kayfooi/ECE4191_T26/CV/checkerboard/checkerboard1.png

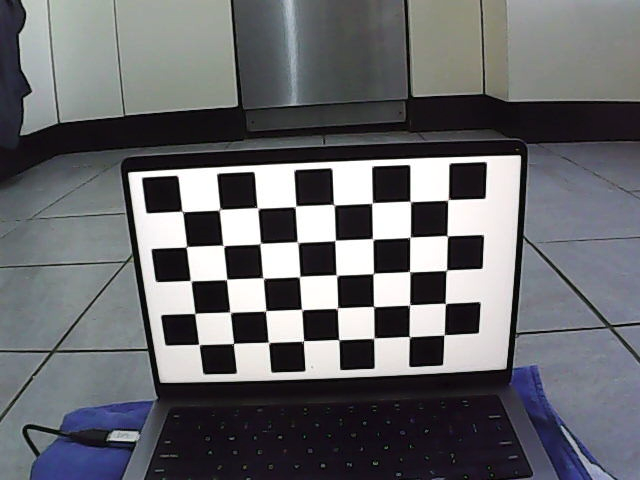
CV/checkerboard/checkerboard1.png
