kayfooi/ECE4191_T26/CV/checkerboard/checkerboard2.png

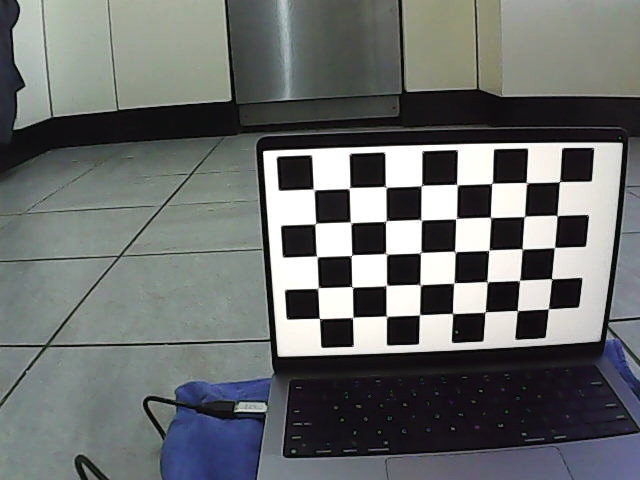
CV/checkerboard/checkerboard2.png
