kayfooi/ECE4191_T26/CV/checkerboard/checkerboard3.png

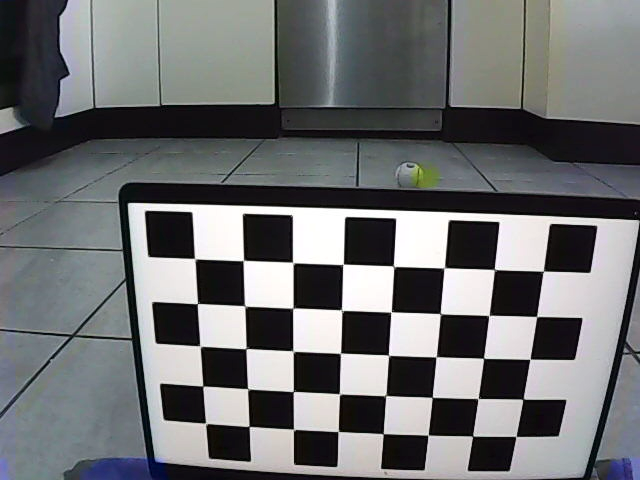
CV/checkerboard/checkerboard3.png
