kayfooi/ECE4191_T26/CV/checkerboard/checkerboard.png

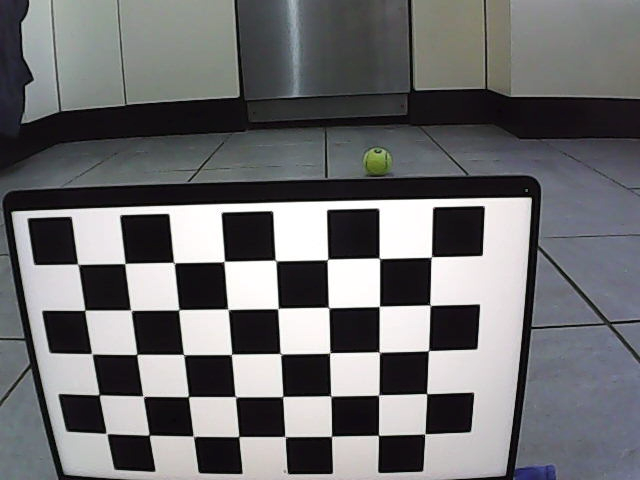
CV/checkerboard/checkerboard.png
