kayfooi/ECE4191_T26/EncoderExplanation for Provided Motor.PNG

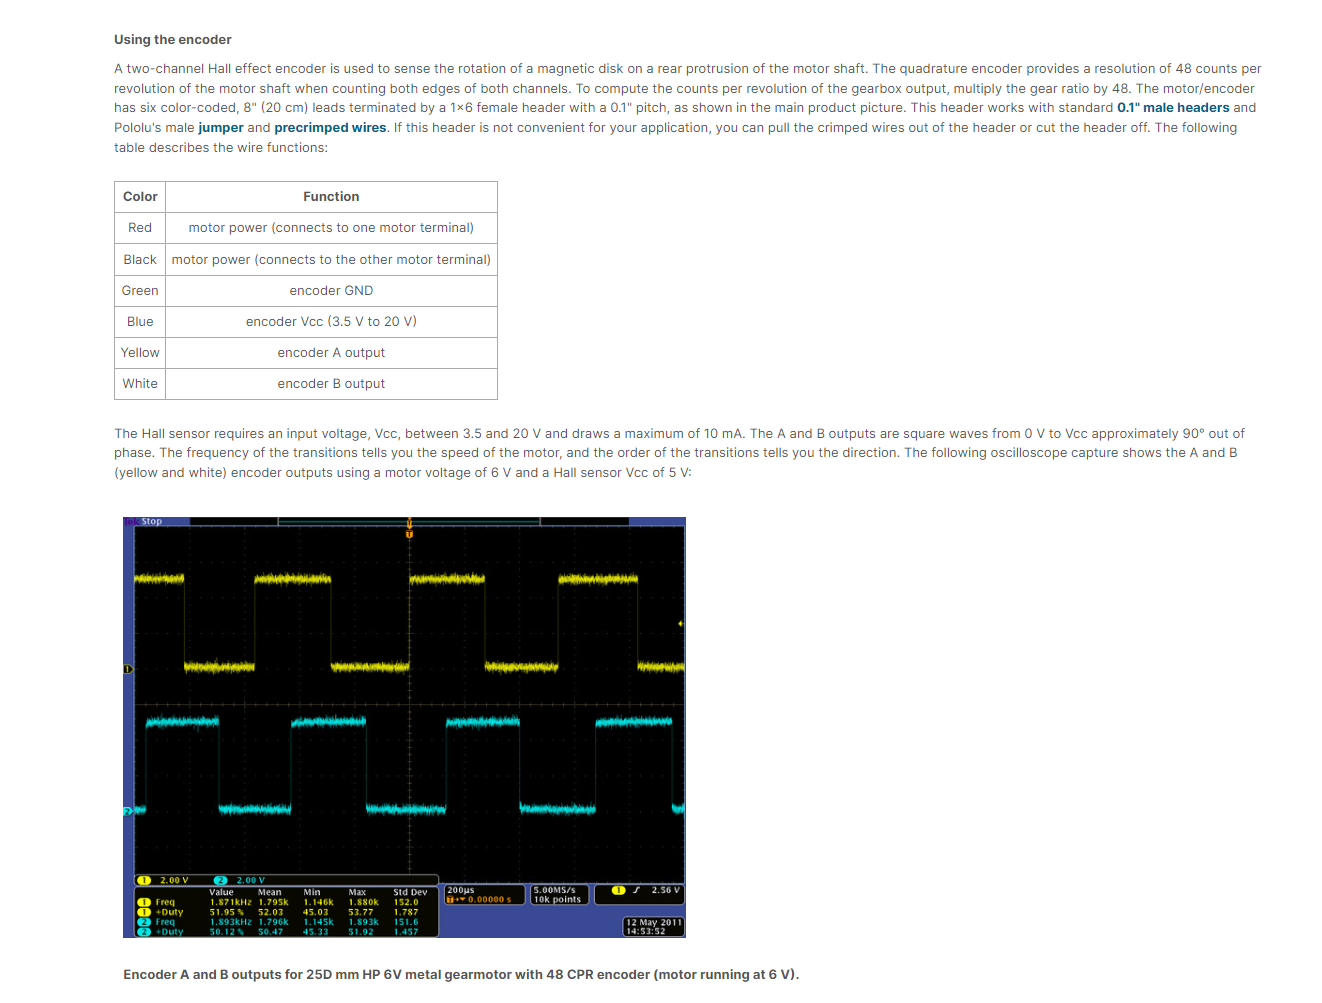
EncoderExplanation for Provided Motor.PNG
