kayfooi/ECE4191_T26/CV/calibration_img.png

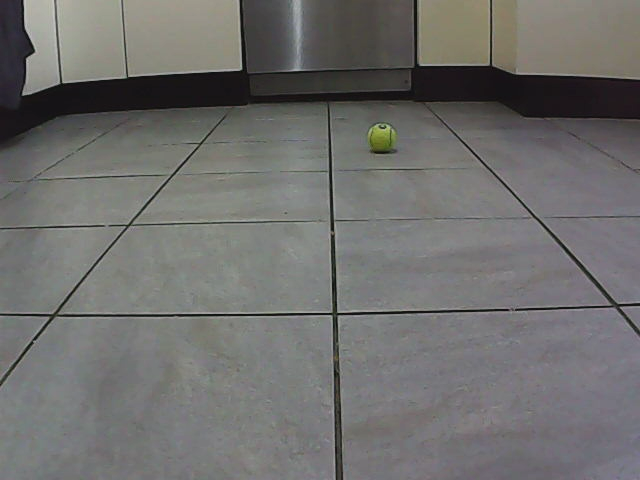
CV/calibration_img.png
