kayfooi/ECE4191_T26/CV/test_imgs/box/0001.jpg

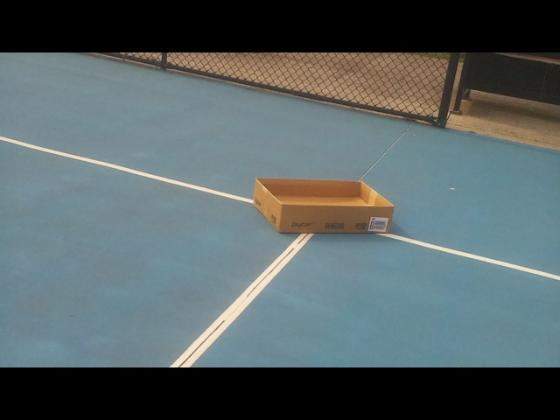
CV/test_imgs/box/0001.jpg
