kayfooi/ECE4191_T26/CV/test_imgs/box/0002.jpg

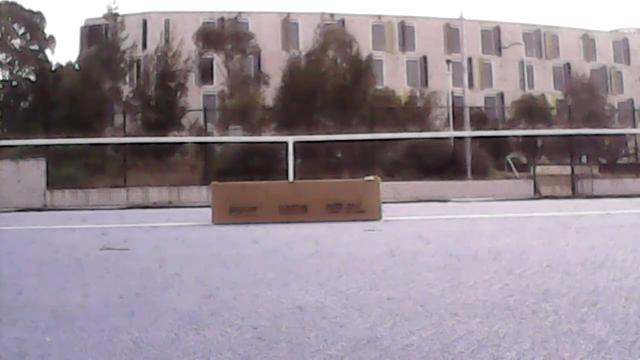
CV/test_imgs/box/0002.jpg
