kayfooi/ECE4191_T26/CV/white_line_detection_result.jpg

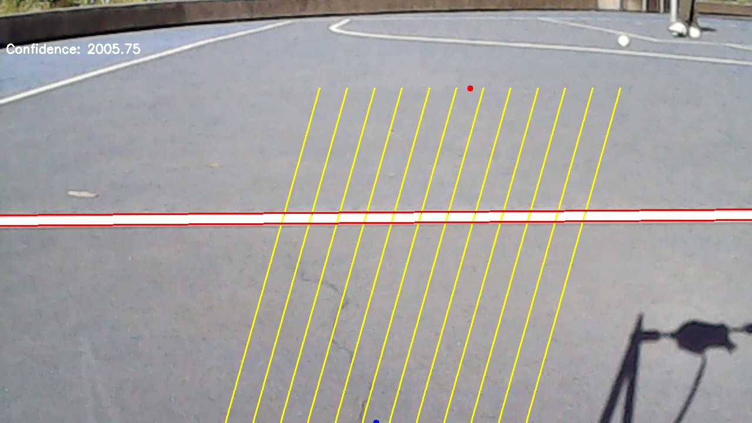
CV/white_line_detection_result.jpg
