kayfooi/ECE4191_T26/test_results/1728355701/line_detect_192_100_200_peaks.jpg

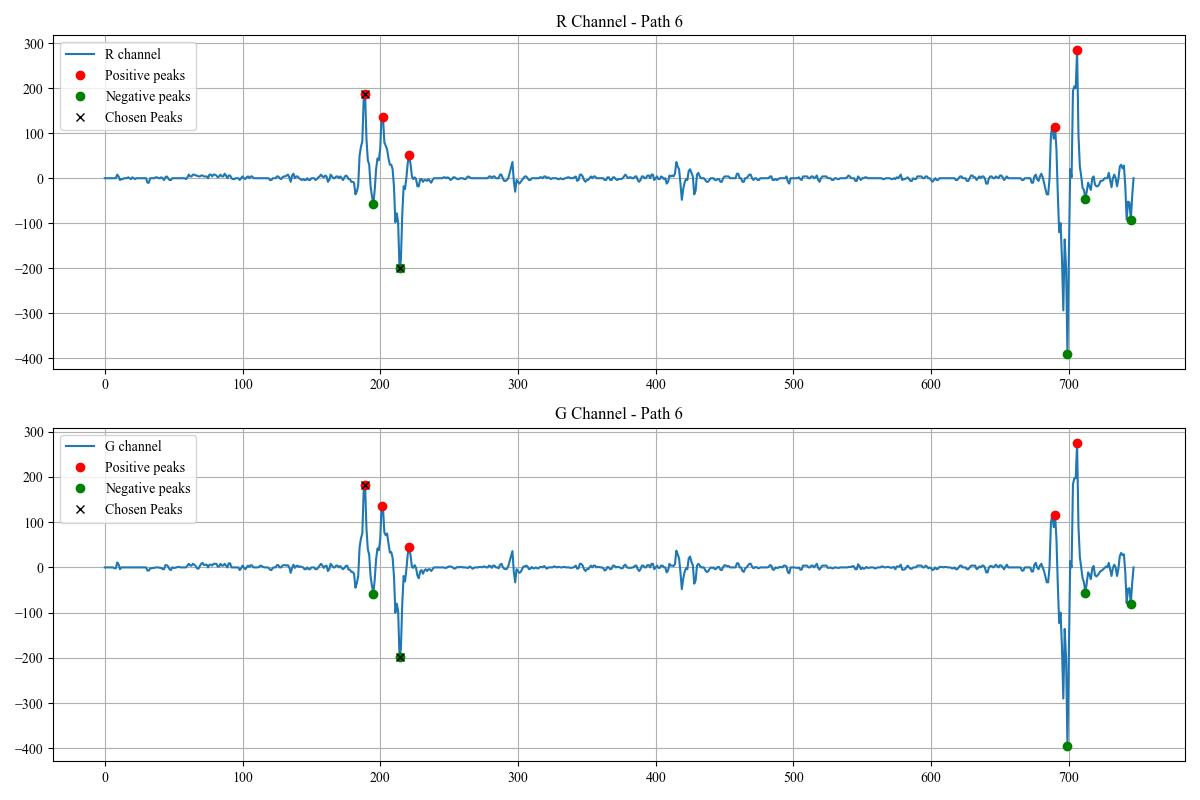
test_results/1728355701/line_detect_192_100_200_peaks.jpg
