kayfooi/ECE4191_T26/test_results/1728355701/line_detect_192_640_200.jpg

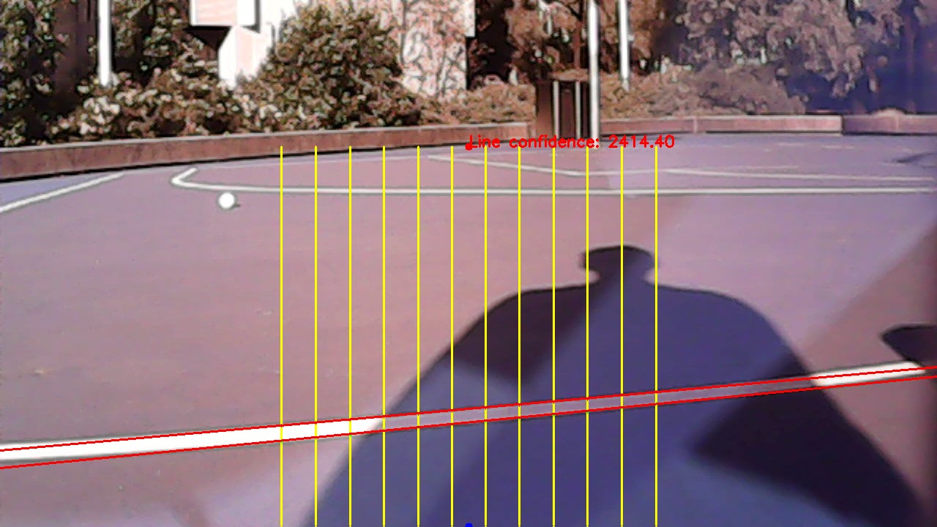
test_results/1728355701/line_detect_192_640_200.jpg
