kayfooi/ECE4191_T26/test_results/1728507664/box_detect_result_0.jpg

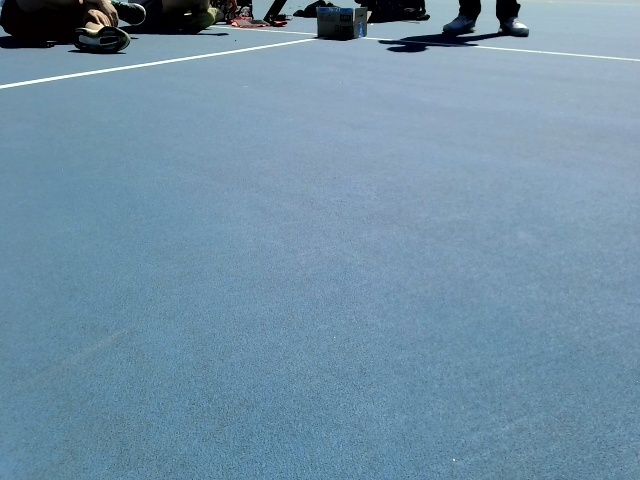
test_results/1728507664/box_detect_result_0.jpg
