kayfooi/ECE4191_T26/test_results/1728507720/box_detect_result_0.jpg

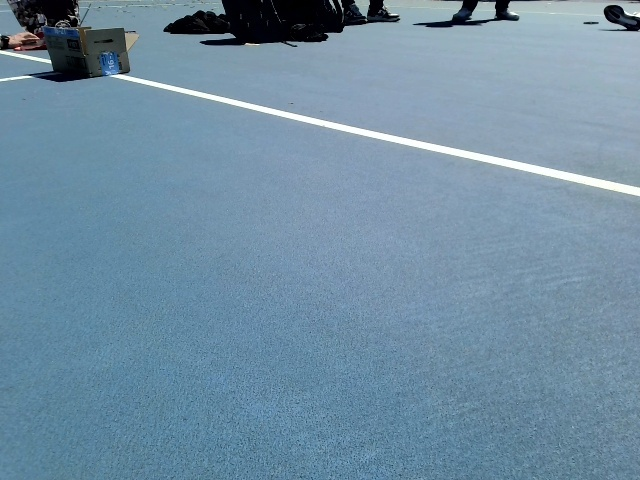
test_results/1728507720/box_detect_result_0.jpg
