kayfooi/ECE4191_T26/test_results/calibration.jpg

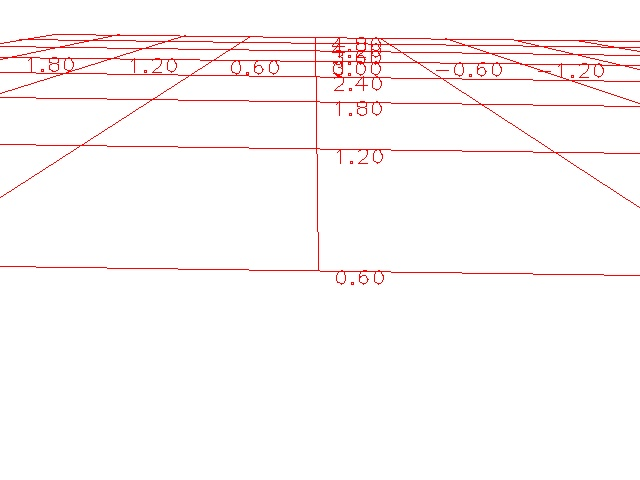
test_results/calibration.jpg
