kayfooi/ECE4191_T26/test_results/detection_image.jpg

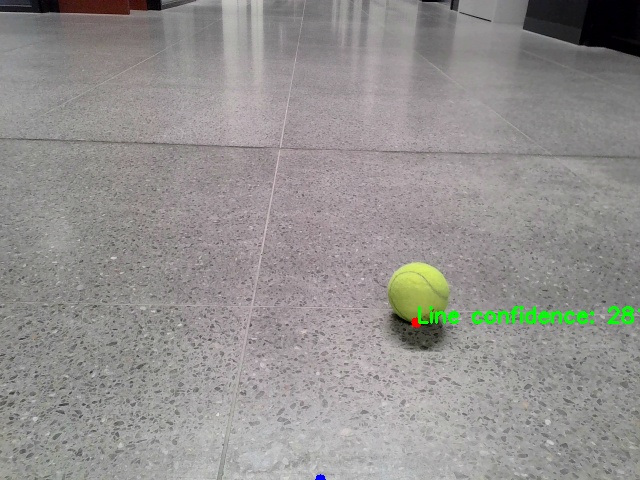
test_results/detection_image.jpg
