kayfooi/ECE4191_T26/test_results/result0.jpg

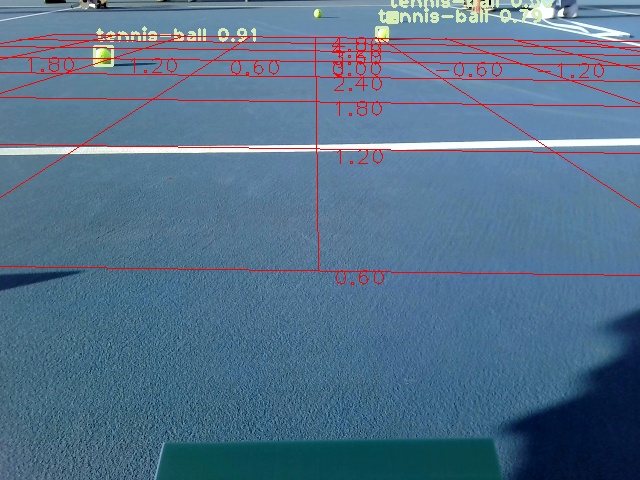
test_results/result0.jpg
