kayfooi/ECE4191_T26/rPi_sensor/laser.py

# laser functions
from PiicoDev_Unified import *

# from laser import laser ! to put in thing that wants to run function
# from time import sleep

# from PiicoDev_VL53L1X import PiicoDev_VL53L1X
# from time import sleep

# distSensor = PiicoDev_VL53L1X()

# while True:
#     dist = distSensor.read() # read the distance in millimetres
#     print(str(dist) + " mm") # convert the number to a string and print
#     sleep(0.1)




# if distance is b/w 0.5m or 1m, obstacle in the way

VL51L1X_DEFAULT_CONFIGURATION = bytes([
0x00, # 0x2d : set bit 2 and 5 to 1 for fast plus mode (1MHz I2C), else don't touch */
0x00, # 0x2e : bit 0 if I2C pulled up at 1.8V, else set bit 0 to 1 (pull up at AVDD) */
0x00, # 0x2f : bit 0 if GPIO pulled up at 1.8V, else set bit 0 to 1 (pull up at AVDD) */
0x01, # 0x30 : set bit 4 to 0 for active high interrupt and 1 for active low (bits 3:0 must be 0x1), use SetInterruptPolarity() */
0x02, # 0x31 : bit 1 = interrupt depending on the polarity, use CheckForDataReady() */
0x00, # 0x32 : not user-modifiable (NUM)*/
0x02, # 0x33 : NUM */
0x08, # 0x34 : NUM */
0x00, # 0x35 : NUM */
0x08, # 0x36 : NUM */
0x10, # 0x37 : NUM */
0x01, # 0x38 : NUM */
0x01, # 0x39 : NUM */
0x00, # 0x3a : NUM */
0x00, # 0x3b : NUM */
0x00, # 0x3c : NUM */
0x00, # 0x3d : NUM */
0xff, # 0x3e : NUM */
0x00, # 0x3f : NUM */
0x0F, # 0x40 : NUM */
0x00, # 0x41 : NUM */
0x00, # 0x42 : NUM */
0x00, # 0x43 : NUM */
0x00, # 0x44 : NUM */
0x00, # 0x45 : NUM */
0x20, # 0x46 : interrupt configuration 0->level low detection, 1-> level high, 2-> Out of window, 3->In window, 0x20-> New sample ready , TBC */
0x0b, # 0x47 : NUM */
0x00, # 0x48 : NUM */
0x00, # 0x49 : NUM */
0x02, # 0x4a : NUM */
0x0a, # 0x4b : NUM */
0x21, # 0x4c : NUM */
0x00, # 0x4d : NUM */
0x00, # 0x4e : NUM */
0x05, # 0x4f : NUM */
0x00, # 0x50 : NUM */
0x00, # 0x51 : NUM */
0x00, # 0x52 : NUM */
0x00, # 0x53 : NUM */
0xc8, # 0x54 : NUM */
0x00, # 0x55 : NUM */
0x00, # 0x56 : NUM */
0x38, # 0x57 : NUM */
0xff, # 0x58 : NUM */
0x01, # 0x59 : NUM */
0x00, # 0x5a : NUM */
0x08, # 0x5b : NUM */
0x00, # 0x5c : NUM */
0x00, # 0x5d : NUM */
0x01, # 0x5e : NUM */
0xdb, # 0x5f : NUM */
0x0f, # 0x60 : NUM */
0x01, # 0x61 : NUM */
0xf1, # 0x62 : NUM */
0x0d, # 0x63 : NUM */
0x01, # 0x64 : Sigma threshold MSB (mm in 14.2 format for MSB+LSB), use SetSigmaThreshold(), default value 90 mm  */
0x68, # 0x65 : Sigma threshold LSB */
0x00, # 0x66 : Min count Rate MSB (MCPS in 9.7 format for MSB+LSB), use SetSignalThreshold() */
0x80, # 0x67 : Min count Rate LSB */
0x08, # 0x68 : NUM */
0xb8, # 0x69 : NUM */
0x00, # 0x6a : NUM */
0x00, # 0x6b : NUM */
0x00, # 0x6c : Intermeasurement period MSB, 32 bits register, use SetIntermeasurementInMs() */
0x00, # 0x6d : Intermeasurement period */
0x0f, # 0x6e : Intermeasurement period */
0x89, # 0x6f : Intermeasurement period LSB */
0x00, # 0x70 : NUM */
0x00, # 0x71 : NUM */
0x00, # 0x72 : distance threshold high MSB (in mm, MSB+LSB), use SetD:tanceThreshold() */
0x00, # 0x73 : distance threshold high LSB */
0x00, # 0x74 : distance threshold low MSB ( in mm, MSB+LSB), use SetD:tanceThreshold() */
0x00, # 0x75 : distance threshold low LSB */
0x00, # 0x76 : NUM */
0x01, # 0x77 : NUM */
0x0f, # 0x78 : NUM */
0x0d, # 0x79 : NUM */
0x0e, # 0x7a : NUM */
0x0e, # 0x7b : NUM */
0x00, # 0x7c : NUM */
0x00, # 0x7d : NUM */
0x02, # 0x7e : NUM */
0xc7, # 0x7f : ROI center, use SetROI() */
0xff, # 0x80 : XY ROI (X=Width, Y=Height), use SetROI() */
0x9B, # 0x81 : NUM */
0x00, # 0x82 : NUM */
0x00, # 0x83 : NUM */
0x00, # 0x84 : NUM */
0x01, # 0x85 : NUM */
0x01, # 0x86 : clear interrupt, use ClearInterrupt() */
0x40  # 0x87 : start ranging, use StartRanging() or StopRanging(), If you want an automatic start after VL53L1X_init() call, put 0x40 in location 0x87 */
])

class PiicoDev_VL53L1X:
    def __init__(self, bus=None, freq=None, sda=None, scl=None, address=0x29):
        try:
            if compat_ind >= 1:
                pass
            else:
                print(compat_str)
        except:
            print(compat_str)
        self.i2c = create_unified_i2c(bus=bus, freq=freq, sda=sda, scl=scl)
        self.addr = address
        self.status = None
        self.reset()
        sleep_ms(1)
        if self.read_model_id() != 0xEACC:
            raise RuntimeError('Failed to find expected ID register values. Check wiring!')
        # write default configuration
        self.i2c.writeto_mem(self.addr, 0x2D, VL51L1X_DEFAULT_CONFIGURATION, addrsize=16)
        sleep_ms(100)
        # the API triggers this change in VL53L1_init_and_start_range() once a
        # measurement is started; assumes MM1 and MM2 are disabled
        self.writeReg16Bit(0x001E, self.readReg16Bit(0x0022) * 4)
        sleep_ms(200)

    def writeReg(self, reg, value):
        return self.i2c.writeto_mem(self.addr, reg, bytes([value]), addrsize=16)
    def writeReg16Bit(self, reg, value):
        return self.i2c.writeto_mem(self.addr, reg, bytes([(value >> 8) & 0xFF, value & 0xFF]), addrsize=16)
    def readReg(self, reg):
        return self.i2c.readfrom_mem(self.addr, reg, 1, addrsize=16)[0]
    def readReg16Bit(self, reg):
        data = self.i2c.readfrom_mem(self.addr, reg, 2, addrsize=16)
        return (data[0]<<8) + data[1]
    def read_model_id(self):
        return self.readReg16Bit(0x010F) 
    def reset(self):
        self.writeReg(0x0000, 0x00)
        sleep_ms(100)
        self.writeReg(0x0000, 0x01)
    
    def read(self):
        try:
            data = self.i2c.readfrom_mem(self.addr, 0x0089, 17, addrsize=16) # RESULT__RANGE_STATUS
        except:
            print(i2c_err_str.format(self.addr))
            return float('NaN')
        range_status = data[0]
        # report_status = data[1]
        stream_count = data[2]
        dss_actual_effective_spads_sd0 = (data[3]<<8) + data[4]
        # peak_signal_count_rate_mcps_sd0 = (data[5]<<8) + data[6]
        ambient_count_rate_mcps_sd0 = (data[7]<<8) + data[8]
        # sigma_sd0 = (data[9]<<8) + data[10]
        # phase_sd0 = (data[11]<<8) + data[12]
        final_crosstalk_corrected_range_mm_sd0 = (data[13]<<8) + data[14]
        peak_signal_count_rate_crosstalk_corrected_mcps_sd0 = (data[15]<<8) + data[16]
        status = None
        if range_status in (17, 2, 1, 3):
            self.status = "HardwareFail"
        elif range_status == 13:
            self.status = "MinRangeFail"
        elif range_status == 18:
            self.status = "SynchronizationInt"
        elif range_status == 5:
            self.status = "OutOfBoundsFail"
        elif range_status == 4:
            self.status = "SignalFail"
        elif range_status == 6:
            self.status = "SignalFail"
        elif range_status == 7:
            self.status = "WrapTargetFail"
        elif range_status == 12:
            self.status = "XtalkSignalFail"
        elif range_status == 8:
            self.status = "RangeValidMinRangeClipped"
        elif range_status == 9:
            if stream_count == 0:
                self.status = "RangeValidNoWrapCheckFail"
            else:
                self.status = "OK"
        return final_crosstalk_corrected_range_mm_sd0
    
    def change_addr(self, new_addr):
        self.writeReg(0x0001, new_addr & 0x7F)
        sleep_ms(50)
        self.addr = new_addr
